XenGi/darling/002.png

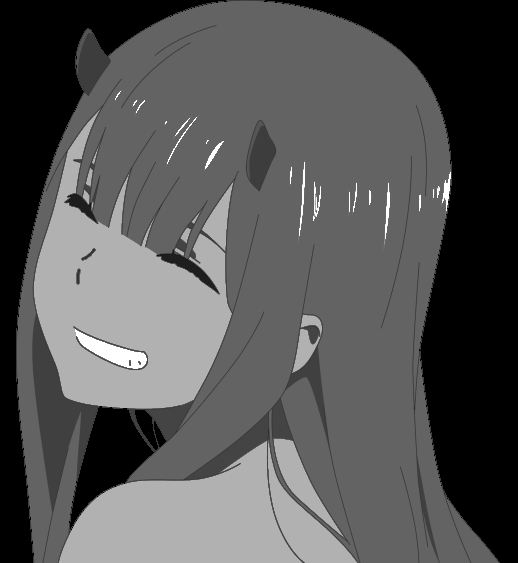
002.png
